Ioana-caty/3d-mechanical-counter/handle3.3mf

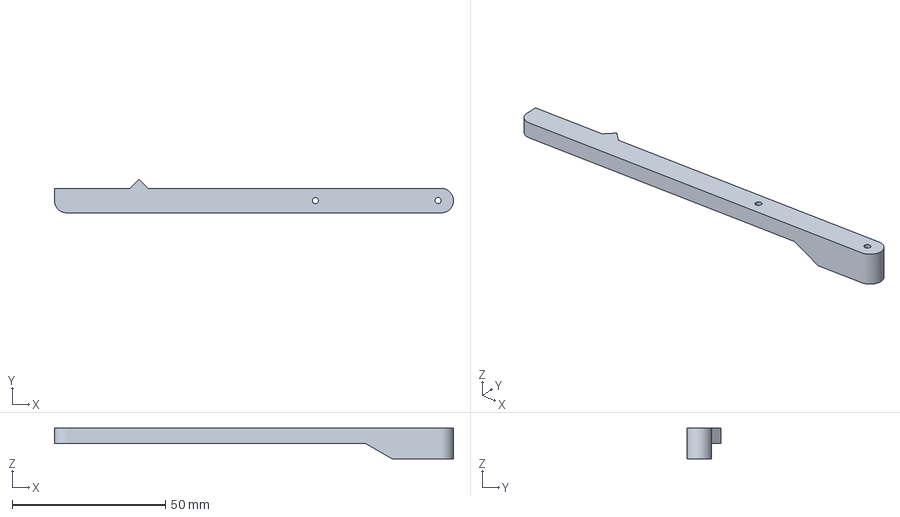
[picture p15: CAD file, 2026-06-05]
handle3.3mf
130.0 x 11.0 x 10.0 mm
