Ioana-caty/3d-mechanical-counter/bottom.3mf

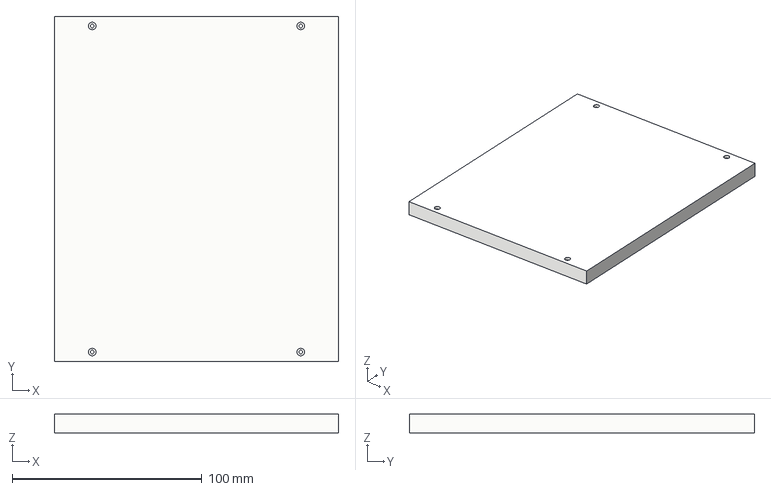
[picture p16: CAD file, 2026-06-05]
bottom.3mf
150.0 x 182.0 x 10.0 mm
