Ioana-caty/3d-mechanical-counter/handle2.3mf

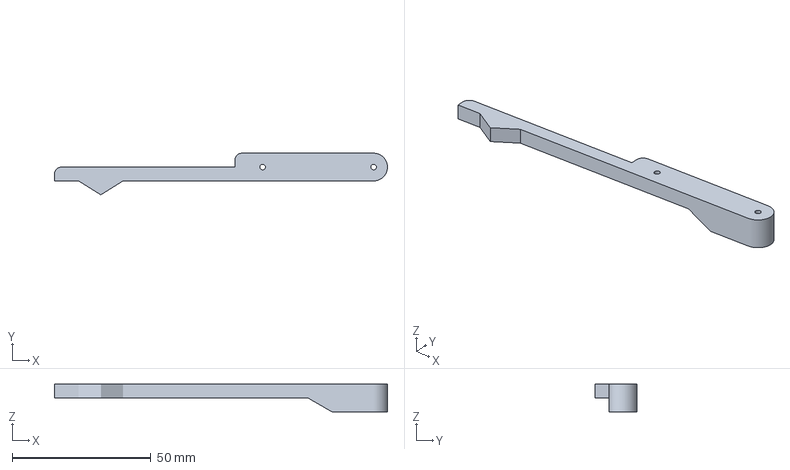
[picture p17: CAD file, 2026-06-05]
handle2.3mf
120.0 x 15.0 x 10.0 mm
