Ioana-caty/3d-mechanical-counter/gear1.3mf

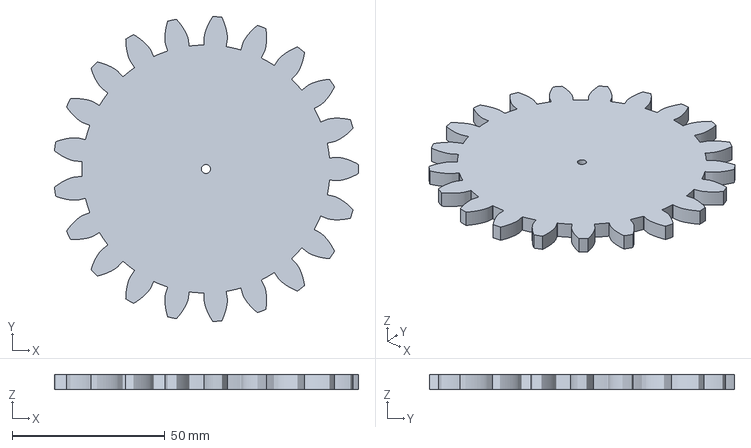
[picture p18: CAD file, 2026-06-05]
gear1.3mf
99.7 x 99.9 x 5.00 mm
