Ioana-caty/3d-mechanical-counter/stick1.3mf

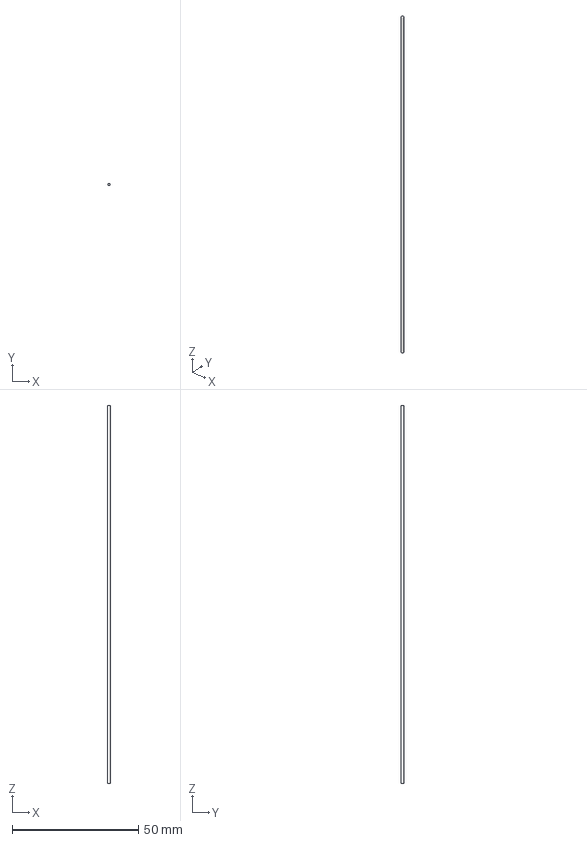
[picture p19: CAD file, 2026-06-05]
stick1.3mf
1.00 x 1.00 x 150.0 mm
